frosty6742/frozen-slimes/Pictures/179157821-9063bb6c-d6fe-42cc-9a80-24e61e10c817.jpg

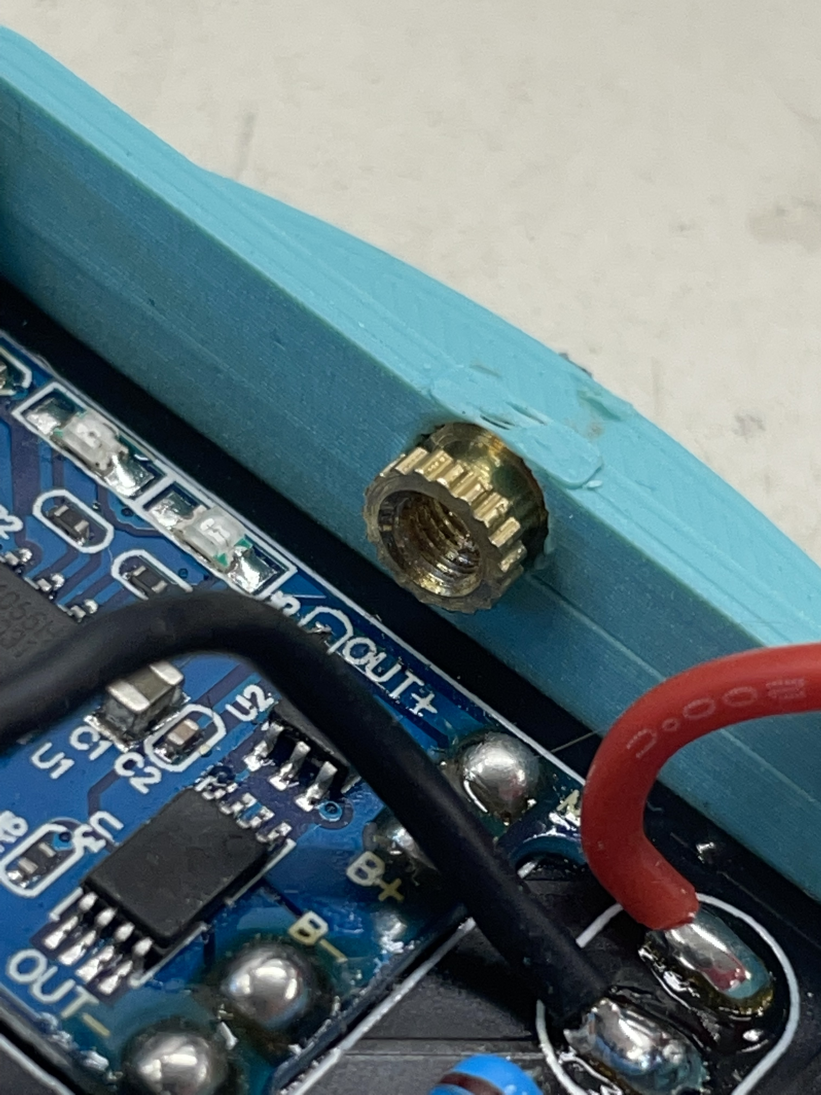
Pictures/179157821-9063bb6c-d6fe-42cc-9a80-24e61e10c817.jpg
